Ning0612/pico-paper-clock/tests/test_presence_memory.py

import importlib.util
import sys
import tempfile
import time
import types
import unittest
from pathlib import Path


class PresenceMemoryTests(unittest.TestCase):
    @classmethod
    def setUpClass(cls):
        cls.original_modules = {
            name: sys.modules.get(name) for name in ("config_manager", "presence_manager")
        }
        cls.original_ticks = {
            name: getattr(time, name, None)
            for name in ("ticks_ms", "ticks_add", "ticks_diff")
        }
        time.ticks_ms = lambda: 1000
        time.ticks_add = lambda value, delta: value + delta
        time.ticks_diff = lambda new, old: new - old

        config_module = types.ModuleType("config_manager")
        config_module.config_manager = types.SimpleNamespace(
            get=lambda _key, default=None: default,
            get_global=lambda key, default=None: (
                "https://discord.com/api/webhooks/test/test"
                if key == "discord_webhook_url" else default
            ),
        )
        cls.config_manager = config_module.config_manager
        sys.modules["config_manager"] = config_module

        source = Path(__file__).resolve().parents[1] / "src" / "presence_manager.py"
        spec = importlib.util.spec_from_file_location("presence_manager", source)
        cls.module = importlib.util.module_from_spec(spec)
        sys.modules["presence_manager"] = cls.module
        spec.loader.exec_module(cls.module)

    @classmethod
    def tearDownClass(cls):
        for name, module in cls.original_modules.items():
            if module is None:
                sys.modules.pop(name, None)
            else:
                sys.modules[name] = module
        for name, value in cls.original_ticks.items():
            if value is None:
                delattr(time, name)
            else:
                setattr(time, name, value)

    def test_enomem_disables_pending_presence_retries(self):
        manager = self.module.PresenceManager(
            discord_sender=lambda _summary: None,
            session_sender=lambda *_args: None,
        )
        manager.pending_summary = "20260713,1,1,1,1"

        self.assertFalse(manager.flush_discord())
        self.assertTrue(manager.discord_disabled)
        self.assertFalse(manager.flush_discord())

    def test_empty_flush_does_not_delay_newly_queued_notification(self):
        original_pending = self.module.PENDING_FILE
        original_session_pending = self.module.PENDING_SESSION_FILE
        try:
            with tempfile.TemporaryDirectory() as directory:
                self.module.PENDING_FILE = str(Path(directory) / "summary.log")
                self.module.PENDING_SESSION_FILE = str(Path(directory) / "session.log")
                sent = []
                manager = self.module.PresenceManager(
                    discord_sender=lambda summary: sent.append(("summary", summary)) or True,
                    session_sender=lambda *values: sent.append(("session", values)) or True,
                )

                self.assertFalse(manager.flush_discord())
                manager._queue_session((
                    "20260715", "090000", "20260715", "090100", 60
                ))

                self.assertTrue(manager.flush_discord())
                self.assertEqual(sent, [("session", (
                    "20260715", "090000", "20260715", "090100", 60
                ))])
        finally:
            self.module.PENDING_FILE = original_pending
            self.module.PENDING_SESSION_FILE = original_session_pending

    def test_low_contiguous_heap_skips_the_send_and_counts_a_failure(self):
        """Below the TLS headroom the attempt is skipped, not burned on ENOMEM."""
        original_probe = self.module._tls_headroom_ok
        original_diag = self.module._diag
        original_largest = self.module._largest_block
        try:
            self.module._tls_headroom_ok = lambda: False
            self.module._largest_block = lambda: 14176
            recorded = []
            self.module._diag = lambda event, detail="": recorded.append((event, detail))

            attempted = []
            manager = self.module.PresenceManager(
                discord_sender=lambda summary: attempted.append(summary) or True,
                session_sender=lambda *values: attempted.append(values) or True,
            )
            manager.pending_summary = "20260725,1,1,1,1"

            self.assertFalse(manager.flush_discord())
            self.assertEqual(attempted, [])
            self.assertEqual(manager.discord_failures, 1)
            self.assertEqual(recorded[0][0], "fail")
            self.assertIn("lowmem", recorded[0][1])
            self.assertIn("largest=14176", recorded[0][1])
        finally:
            self.module._tls_headroom_ok = original_probe
            self.module._diag = original_diag
            self.module._largest_block = original_largest

    def test_repeated_failures_accumulate_but_logging_is_throttled(self):
        original_probe = self.module._tls_headroom_ok
        original_diag = self.module._diag
        original_largest = self.module._largest_block
        try:
            self.module._tls_headroom_ok = lambda: False
            self.module._largest_block = lambda: 0
            recorded = []
            self.module._diag = lambda event, detail="": recorded.append((event, detail))

            manager = self.module.PresenceManager(
                discord_sender=lambda _summary: True,
                session_sender=lambda *_values: True,
            )
            manager.pending_summary = "20260725,1,1,1,1"

            for _ in range(30):
                # Re-arm the 60 s throttle so each loop is a real attempt.
                manager.last_retry_ms = time.ticks_add(time.ticks_ms(), -600001)
                manager.flush_discord()

            self.assertEqual(manager.discord_failures, 30)
            # First failure, then every tenth: 1, 10, 20, 30.
            self.assertEqual(len(recorded), 4)
        finally:
            self.module._tls_headroom_ok = original_probe
            self.module._diag = original_diag
            self.module._largest_block = original_largest

    def test_successful_flush_clears_the_stall_counter(self):
        original_paths = {
            name: getattr(self.module, name)
            for name in ("PENDING_FILE", "PENDING_SESSION_FILE")
        }
        original_diag = self.module._diag
        try:
            with tempfile.TemporaryDirectory() as directory:
                self.module.PENDING_FILE = str(Path(directory) / "summary.log")
                self.module.PENDING_SESSION_FILE = str(Path(directory) / "session.log")
                recorded = []
                self.module._diag = lambda event, detail="": recorded.append((event, detail))

                manager = self.module.PresenceManager(
                    discord_sender=lambda _summary: True,
                    session_sender=lambda *_values: True,
                )
                manager.pending_summary = "20260725,1,1,1,1"
                manager.discord_failures = 17

                self.assertTrue(manager.flush_discord())
                self.assertEqual(manager.discord_failures, 0)
                self.assertEqual(recorded[-1][0], "recovered")
                self.assertIn("after=17", recorded[-1][1])
        finally:
            for name, value in original_paths.items():
                setattr(self.module, name, value)
            self.module._diag = original_diag

    def test_only_memory_failures_feed_the_reboot_counter(self):
        """HTTP/network failures must not accumulate toward an auto-reset."""
        original_probe = self.module._tls_headroom_ok
        original_diag = self.module._diag
        original_reason = self.module._last_failure_reason
        try:
            self.module._tls_headroom_ok = lambda: True
            self.module._diag = lambda event, detail="": None

            manager = self.module.PresenceManager(
                discord_sender=lambda _summary: False,
                session_sender=lambda *_values: False,
            )
            manager.pending_summary = "20260725,1,1,1,1"

            self.module._last_failure_reason = lambda: "http404"
            for _ in range(5):
                manager.last_retry_ms = time.ticks_add(time.ticks_ms(), -600001)
                manager.flush_discord()
            self.assertEqual(manager.discord_failures, 5)
            self.assertEqual(manager.discord_mem_failures, 0)

            self.module._last_failure_reason = lambda: "enomem"
            for _ in range(3):
                manager.last_retry_ms = time.ticks_add(time.ticks_ms(), -600001)
                manager.flush_discord()
            self.assertEqual(manager.discord_mem_failures, 3)

            # A non-memory failure breaks the memory streak.
            self.module._last_failure_reason = lambda: "offline"
            manager.last_retry_ms = time.ticks_add(time.ticks_ms(), -600001)
            manager.flush_discord()
            self.assertEqual(manager.discord_mem_failures, 0)
        finally:
            self.module._tls_headroom_ok = original_probe
            self.module._diag = original_diag
            self.module._last_failure_reason = original_reason

    def test_memory_failure_on_either_pending_counts_for_recovery(self):
        """With two pendings failing differently, memory starvation must still count."""
        original_probe = self.module._tls_headroom_ok
        original_diag = self.module._diag
        original_reason = self.module._last_failure_reason
        original_paths = {
            name: getattr(self.module, name)
            for name in ("PENDING_FILE", "PENDING_SESSION_FILE")
        }
        try:
            with tempfile.TemporaryDirectory() as directory:
                self.module.PENDING_FILE = str(Path(directory) / "summary.log")
                self.module.PENDING_SESSION_FILE = str(Path(directory) / "session.log")
                self.module._tls_headroom_ok = lambda: True
                self.module._diag = lambda event, detail="": None

                manager = self.module.PresenceManager(
                    discord_sender=lambda _summary: False,
                    session_sender=lambda *_values: False,
                )
                manager.pending_summary = "20260725,1,1,1,1"
                manager.pending_session = "20260725,090000,20260725,090100,60"

                # First attempt reports ENOMEM, the second reports HTTP 404.
                reasons = iter(("enomem", "http404"))
                self.module._last_failure_reason = lambda: next(reasons, "http404")

                manager.last_retry_ms = time.ticks_add(time.ticks_ms(), -600001)
                manager.flush_discord()
                self.assertEqual(manager.discord_mem_failures, 1)
        finally:
            for name, value in original_paths.items():
                setattr(self.module, name, value)
            self.module._tls_headroom_ok = original_probe
            self.module._diag = original_diag
            self.module._last_failure_reason = original_reason

    def test_persist_failure_flag_is_sticky_across_successful_flushes(self):
        """An emptied queue is not proof of health - it may be the loss itself."""
        original_paths = {
            name: getattr(self.module, name)
            for name in ("PENDING_FILE", "PENDING_SESSION_FILE")
        }
        original_probe = self.module._tls_headroom_ok
        original_diag = self.module._diag
        try:
            with tempfile.TemporaryDirectory() as directory:
                self.module.PENDING_FILE = str(Path(directory) / "summary.log")
                self.module.PENDING_SESSION_FILE = str(Path(directory) / "session.log")
                self.module._tls_headroom_ok = lambda: True
                self.module._diag = lambda event, detail="": None

                manager = self.module.PresenceManager(
                    discord_sender=lambda _summary: True,
                    session_sender=lambda *_values: True,
                )
                manager.pending_persist_failed = True
                manager.pending_summary = "20260725,1,1,1,1"

                manager.last_retry_ms = time.ticks_add(time.ticks_ms(), -600001)
                self.assertTrue(manager.flush_discord())
                self.assertIsNone(manager.pending_summary)
                self.assertTrue(manager.pending_persist_failed)
        finally:
            for name, value in original_paths.items():
                setattr(self.module, name, value)
            self.module._tls_headroom_ok = original_probe
            self.module._diag = original_diag

    def test_pending_persist_failure_is_recorded(self):
        """A queue write that never reached flash must be visible to the caller."""
        original_paths = {
            name: getattr(self.module, name)
            for name in ("PENDING_FILE", "PENDING_SESSION_FILE")
        }
        try:
            self.module.PENDING_FILE = str(Path("no-such-dir") / "nested" / "summary.log")
            self.module.PENDING_SESSION_FILE = str(Path("no-such-dir") / "nested" / "session.log")
            manager = self.module.PresenceManager(
                discord_sender=lambda _summary: True,
                session_sender=lambda *_values: True,
            )
            self.assertFalse(manager.pending_persist_failed)
            manager._queue_summary("20260725,1,1,1,1")
            self.assertTrue(manager.pending_persist_failed)
            # The notification is still held in RAM so it can still be delivered.
            self.assertEqual(manager.pending_summary, "20260725,1,1,1,1")
        finally:
            for name, value in original_paths.items():
                setattr(self.module, name, value)

    def test_missing_webhook_is_not_misfiled_as_memory_starvation(self):
        """A reboot cannot conjure up a webhook, so this must not drive one."""
        original_probe = self.module._tls_headroom_ok
        original_blocked = self.module._delivery_blocked
        original_diag = self.module._diag
        try:
            # Memory is starved *and* delivery is impossible for another reason.
            self.module._tls_headroom_ok = lambda: False
            self.module._delivery_blocked = lambda: "nowebhook"
            recorded = []
            self.module._diag = lambda event, detail="": recorded.append((event, detail))

            attempted = []
            manager = self.module.PresenceManager(
                discord_sender=lambda summary: attempted.append(summary) or True,
                session_sender=lambda *values: attempted.append(values) or True,
            )
            manager.pending_summary = "20260725,1,1,1,1"

            for _ in range(5):
                manager.last_retry_ms = time.ticks_add(time.ticks_ms(), -600001)
                self.assertFalse(manager.flush_discord())

            self.assertEqual(attempted, [])
            self.assertEqual(manager.discord_failures, 5)
            self.assertEqual(manager.discord_mem_failures, 0)
            self.assertIn("nowebhook", recorded[0][1])
        finally:
            self.module._tls_headroom_ok = original_probe
            self.module._delivery_blocked = original_blocked
            self.module._diag = original_diag

    def test_offline_is_not_misfiled_as_memory_starvation(self):
        original_probe = self.module._tls_headroom_ok
        original_blocked = self.module._delivery_blocked
        original_diag = self.module._diag
        try:
            self.module._tls_headroom_ok = lambda: False
            self.module._delivery_blocked = lambda: "offline"
            self.module._diag = lambda event, detail="": None

            manager = self.module.PresenceManager(
                discord_sender=lambda _summary: True,
                session_sender=lambda *_values: True,
            )
            manager.pending_summary = "20260725,1,1,1,1"
            manager.discord_mem_failures = 7

            manager.last_retry_ms = time.ticks_add(time.ticks_ms(), -600001)
            self.assertFalse(manager.flush_discord())
            self.assertEqual(manager.discord_mem_failures, 0)
        finally:
            self.module._tls_headroom_ok = original_probe
            self.module._delivery_blocked = original_blocked
            self.module._diag = original_diag

    def test_delivery_precondition_defaults_to_attempting_the_send(self):
        """If the probe cannot run it must never be the reason nothing is sent."""
        self.assertEqual(self.module._delivery_blocked(), "")

    def test_missing_webhook_does_not_import_notifier(self):
        original_get_global = self.config_manager.get_global
        original_notifier = sys.modules.pop("discord_notifier", None)
        try:
            self.config_manager.get_global = lambda _key, default=None: default
            self.assertEqual(self.module._delivery_blocked(), "nowebhook")
            self.assertNotIn("discord_notifier", sys.modules)
        finally:
            self.config_manager.get_global = original_get_global
            if original_notifier is not None:
                sys.modules["discord_notifier"] = original_notifier

    def test_headroom_probe_defaults_to_allowing_the_send(self):
        """A probe that cannot run must never be the reason a message is blocked."""
        self.assertTrue(self.module._tls_headroom_ok())

    def test_startup_flush_drains_pending_session_and_summary_files(self):
        original_pending = self.module.PENDING_FILE
        original_session_pending = self.module.PENDING_SESSION_FILE
        try:
            with tempfile.TemporaryDirectory() as directory:
                self.module.PENDING_FILE = str(Path(directory) / "summary.log")
                self.module.PENDING_SESSION_FILE = str(Path(directory) / "session.log")
                Path(self.module.PENDING_FILE).write_text("20260715,1,1,1,1\n", encoding="utf-8")
                Path(self.module.PENDING_SESSION_FILE).write_text(
                    "20260715,090000,20260715,090100,60\n", encoding="utf-8"
                )
                sent = []
                manager = self.module.PresenceManager(
                    discord_sender=lambda summary: sent.append(("summary", summary)) or True,
                    session_sender=lambda *values: sent.append(("session", values)) or True,
                )

                self.assertEqual(manager.flush_startup_discord(), 2)
                self.assertEqual([kind for kind, _value in sent], ["session", "summary"])
                self.assertEqual(Path(self.module.PENDING_FILE).read_text(encoding="utf-8"), "")
                self.assertEqual(Path(self.module.PENDING_SESSION_FILE).read_text(encoding="utf-8"), "")
        finally:
            self.module.PENDING_FILE = original_pending
            self.module.PENDING_SESSION_FILE = original_session_pending

    def test_daily_retention_covers_year_heatmap_without_extending_events(self):
        original_paths = {
            name: getattr(self.module, name)
            for name in ("PENDING_FILE", "PENDING_SESSION_FILE")
        }
        try:
            with tempfile.TemporaryDirectory() as directory:
                self.module.PENDING_FILE = str(Path(directory) / "summary.log")
                self.module.PENDING_SESSION_FILE = str(Path(directory) / "session.log")

                manager = self.module.PresenceManager(
                    discord_sender=lambda _summary: None,
                    session_sender=lambda *_args: None,
                )
                calls = []
                original_trim = self.module._trim_by_date
                original_mktime = self.module.time.mktime
                self.module._trim_by_date = lambda path, date: calls.append((path, date))
                self.module.time.mktime = lambda value: original_mktime(tuple(value) + (0,))
                try:
                    manager._trim_retention("20260714")
                finally:
                    self.module._trim_by_date = original_trim
                    self.module.time.mktime = original_mktime

                self.assertEqual([path for path, _date in calls], [
                    self.module.EVENT_FILE,
                    self.module.DAILY_FILE,
                    self.module.PENDING_FILE,
                    self.module.PENDING_SESSION_FILE,
                ])
                self.assertLess(calls[1][1], calls[0][1])
                self.assertGreater(calls[2][1], calls[0][1])
                self.assertEqual(calls[2][1], calls[3][1])
        finally:
            for name, value in original_paths.items():
                setattr(self.module, name, value)

    def test_pending_retention_drops_stale_notifications_and_refreshes_head(self):
        original_paths = {
            name: getattr(self.module, name)
            for name in ("EVENT_FILE", "DAILY_FILE", "PENDING_FILE", "PENDING_SESSION_FILE")
        }
        original_mktime = self.module.time.mktime
        try:
            with tempfile.TemporaryDirectory() as directory:
                root = Path(directory)
                self.module.EVENT_FILE = str(root / "events.log")
                self.module.DAILY_FILE = str(root / "daily.log")
                self.module.PENDING_FILE = str(root / "summary.log")
                self.module.PENDING_SESSION_FILE = str(root / "session.log")
                Path(self.module.PENDING_FILE).write_text(
                    "20260601,1,1,1,1\n20260714,1,1,1,1\n", encoding="utf-8"
                )
                Path(self.module.PENDING_SESSION_FILE).write_text(
                    "20260601,090000,20260601,090100,60\n"
                    "20260714,090000,20260714,090100,60\n",
                    encoding="utf-8",
                )
                self.module.time.mktime = lambda value: original_mktime(tuple(value) + (0,))

                manager = self.module.PresenceManager(
                    discord_sender=lambda _summary: None,
                    session_sender=lambda *_args: None,
                )
                manager._trim_retention("20260714")

                self.assertEqual(
                    Path(self.module.PENDING_FILE).read_text(encoding="utf-8").splitlines(),
                    ["20260714,1,1,1,1"],
                )
                self.assertEqual(
                    Path(self.module.PENDING_SESSION_FILE).read_text(encoding="utf-8").splitlines(),
                    ["20260714,090000,20260714,090100,60"],
                )
                self.assertEqual(manager.pending_summary, "20260714,1,1,1,1")
                self.assertEqual(
                    manager.pending_session, "20260714,090000,20260714,090100,60"
                )
        finally:
            self.module.time.mktime = original_mktime
            for name, value in original_paths.items():
                setattr(self.module, name, value)

    def test_status_exposes_device_current_date_for_web_clients(self):
        manager = self.module.PresenceManager(
            discord_sender=lambda _summary: None,
            session_sender=lambda *_args: None,
        )
        manager.current_date = "20260715"

        self.assertEqual(manager.get_status()["current_date"], "20260715")

    def test_read_lines_keeps_only_recent_entries(self):
        original_event_file = self.module.EVENT_FILE
        original_daily_file = self.module.DAILY_FILE
        try:
            with tempfile.TemporaryDirectory() as directory:
                event_file = Path(directory) / "events.log"
                daily_file = Path(directory) / "daily.log"
                event_file.write_text(
                    "\n".join(["x" * 257] + [
                        "event-{}".format(index) for index in range(140)
                    ]) + "\n",
                    encoding="utf-8",
                )
                daily_file.write_text(
                    "\n".join("daily-{}".format(index) for index in range(380)) + "\n",
                    encoding="utf-8",
                )
                self.module.EVENT_FILE = str(event_file)
                self.module.DAILY_FILE = str(daily_file)

                events = self.module._read_lines(self.module.EVENT_FILE)
                daily = self.module._read_lines(self.module.DAILY_FILE)

                self.assertEqual(len(events), self.module.MAX_EVENT_LINES_IN_MEMORY)
                self.assertNotIn("x" * 257, events)
                self.assertEqual(events[0], "event-12")
                self.assertEqual(events[-1], "event-139")
                self.assertEqual(len(daily), self.module.MAX_DAILY_LINES_IN_MEMORY)
                self.assertEqual(daily[0], "daily-14")
                self.assertEqual(daily[-1], "daily-379")
        finally:
            self.module.EVENT_FILE = original_event_file
            self.module.DAILY_FILE = original_daily_file

    def test_away_and_return_states_wait_for_independent_timeouts(self):
        original_paths = {
            name: getattr(self.module, name)
            for name in ("EVENT_FILE", "DAILY_FILE", "PENDING_FILE", "PENDING_SESSION_FILE")
        }
        original_mktime = self.module.time.mktime

        def local_time(seconds):
            hours, remainder = divmod(seconds, 3600)
            minutes, seconds = divmod(remainder, 60)
            return (2026, 7, 15, hours, minutes, seconds, 2, 0)

        try:
            with tempfile.TemporaryDirectory() as directory:
                root = Path(directory)
                self.module.EVENT_FILE = str(root / "events.log")
                self.module.DAILY_FILE = str(root / "daily.log")
                self.module.PENDING_FILE = str(root / "summary.log")
                self.module.PENDING_SESSION_FILE = str(root / "session.log")
                self.module.time.mktime = lambda value: value[3] * 3600 + value[4] * 60 + value[5]

                manager = self.module.PresenceManager()
                manager.update(100, 200, local_time(0), 180, 10)
                manager.update(300, 200, local_time(120), 180, 10)
                self.assertEqual(manager.get_status()["state"], 1)
                manager.update(100, 200, local_time(150), 180, 10)
                self.assertEqual(manager.get_status()["state"], 1)

                manager.update(300, 200, local_time(180), 180, 10)
                manager.update(300, 200, local_time(360), 180, 10)
                self.assertEqual(manager.get_status()["state"], 0)
                manager.update(100, 200, local_time(361), 180)
                self.assertEqual(manager.get_status()["state"], 0)
                manager.update(100, 200, local_time(370), 180)
                self.assertEqual(manager.get_status()["state"], 0)
                manager.update(100, 200, local_time(371), 180)
                self.assertEqual(manager.get_status()["state"], 1)

                self.assertEqual(
                    [line.split(",")[2] for line in Path(self.module.EVENT_FILE).read_text().splitlines()],
                    ["1", "0", "1"],
                )
        finally:
            self.module.time.mktime = original_mktime
            for name, value in original_paths.items():
                setattr(self.module, name, value)

    def test_update_reports_only_confirmed_away_transition(self):
        original_paths = {
            name: getattr(self.module, name)
            for name in ("EVENT_FILE", "DAILY_FILE", "PENDING_FILE", "PENDING_SESSION_FILE")
        }
        original_mktime = self.module.time.mktime

        def local_time(seconds):
            hours, remainder = divmod(seconds, 3600)
            minutes, seconds = divmod(remainder, 60)
            return (2026, 7, 15, hours, minutes, seconds, 2, 0)

        try:
            with tempfile.TemporaryDirectory() as directory:
                root = Path(directory)
                self.module.EVENT_FILE = str(root / "events.log")
                self.module.DAILY_FILE = str(root / "daily.log")
                self.module.PENDING_FILE = str(root / "summary.log")
                self.module.PENDING_SESSION_FILE = str(root / "session.log")
                self.module.time.mktime = lambda value: value[3] * 3600 + value[4] * 60 + value[5]

                manager = self.module.PresenceManager()
                self.assertFalse(manager.update(100, 200, local_time(0), 3, 10))
                self.assertFalse(manager.update(300, 200, local_time(1), 3, 10))
                self.assertTrue(manager.update(300, 200, local_time(4), 3, 10))
                self.assertFalse(manager.update(300, 200, local_time(5), 3, 10))
        finally:
            self.module.time.mktime = original_mktime
            for name, value in original_paths.items():
                setattr(self.module, name, value)

    def test_restored_open_session_starts_away_timeout_from_first_sample(self):
        original_paths = {
            name: getattr(self.module, name)
            for name in ("EVENT_FILE", "DAILY_FILE", "PENDING_FILE", "PENDING_SESSION_FILE")
        }
        original_mktime = self.module.time.mktime

        def local_time(seconds):
            hours, remainder = divmod(seconds, 3600)
            minutes, seconds = divmod(remainder, 60)
            return (2026, 7, 15, hours, minutes, seconds, 2, 0)

        try:
            with tempfile.TemporaryDirectory() as directory:
                root = Path(directory)
                self.module.EVENT_FILE = str(root / "events.log")
                self.module.DAILY_FILE = str(root / "daily.log")
                self.module.PENDING_FILE = str(root / "summary.log")
                self.module.PENDING_SESSION_FILE = str(root / "session.log")
                Path(self.module.EVENT_FILE).write_text("20260715,000000,1,100\n", encoding="utf-8")
                self.module.time.mktime = lambda value: value[3] * 3600 + value[4] * 60 + value[5]

                manager = self.module.PresenceManager()
                manager.update(300, 200, local_time(600), 180, 10)
                self.assertEqual(manager.get_status()["state"], 1)
                manager.update(300, 200, local_time(780), 180, 10)
                self.assertEqual(manager.get_status()["state"], 0)
        finally:
            self.module.time.mktime = original_mktime
            for name, value in original_paths.items():
                setattr(self.module, name, value)

    def test_restored_away_state_waits_for_return_timeout(self):
        original_paths = {
            name: getattr(self.module, name)
            for name in ("EVENT_FILE", "DAILY_FILE", "PENDING_FILE", "PENDING_SESSION_FILE")
        }
        original_mktime = self.module.time.mktime

        def local_time(seconds):
            hours, remainder = divmod(seconds, 3600)
            minutes, seconds = divmod(remainder, 60)
            return (2026, 7, 15, hours, minutes, seconds, 2, 0)

        try:
            with tempfile.TemporaryDirectory() as directory:
                root = Path(directory)
                self.module.EVENT_FILE = str(root / "events.log")
                self.module.DAILY_FILE = str(root / "daily.log")
                self.module.PENDING_FILE = str(root / "summary.log")
                self.module.PENDING_SESSION_FILE = str(root / "session.log")
                Path(self.module.EVENT_FILE).write_text("20260715,000000,0,300\n", encoding="utf-8")
                self.module.time.mktime = lambda value: value[3] * 3600 + value[4] * 60 + value[5]

                manager = self.module.PresenceManager()
                manager.update(100, 200, local_time(600), 180, 10)
                self.assertEqual(manager.get_status()["state"], 0)
                manager.update(100, 200, local_time(609), 180, 10)
                self.assertEqual(manager.get_status()["state"], 0)
                manager.update(100, 200, local_time(610), 180, 10)
                self.assertEqual(manager.get_status()["state"], 1)
        finally:
            self.module.time.mktime = original_mktime
            for name, value in original_paths.items():
                setattr(self.module, name, value)


if __name__ == "__main__":
    unittest.main()
